HectorJRL/storymaker_dev/firmware/data/pluma.png

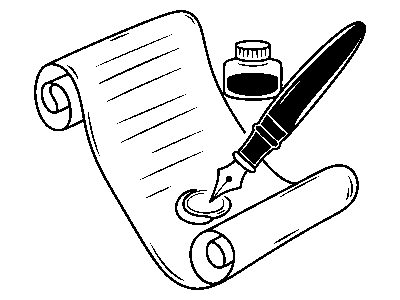
firmware/data/pluma.png
